automated-ultramicrotomy/embl-system/Images/box-images/box-1.jpg

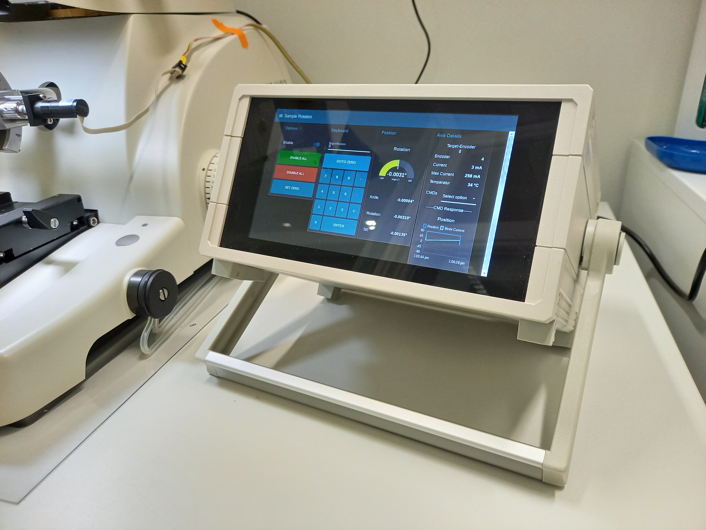
Images/box-images/box-1.jpg
