automated-ultramicrotomy/embl-system/Images/box-images/box-2.jpg

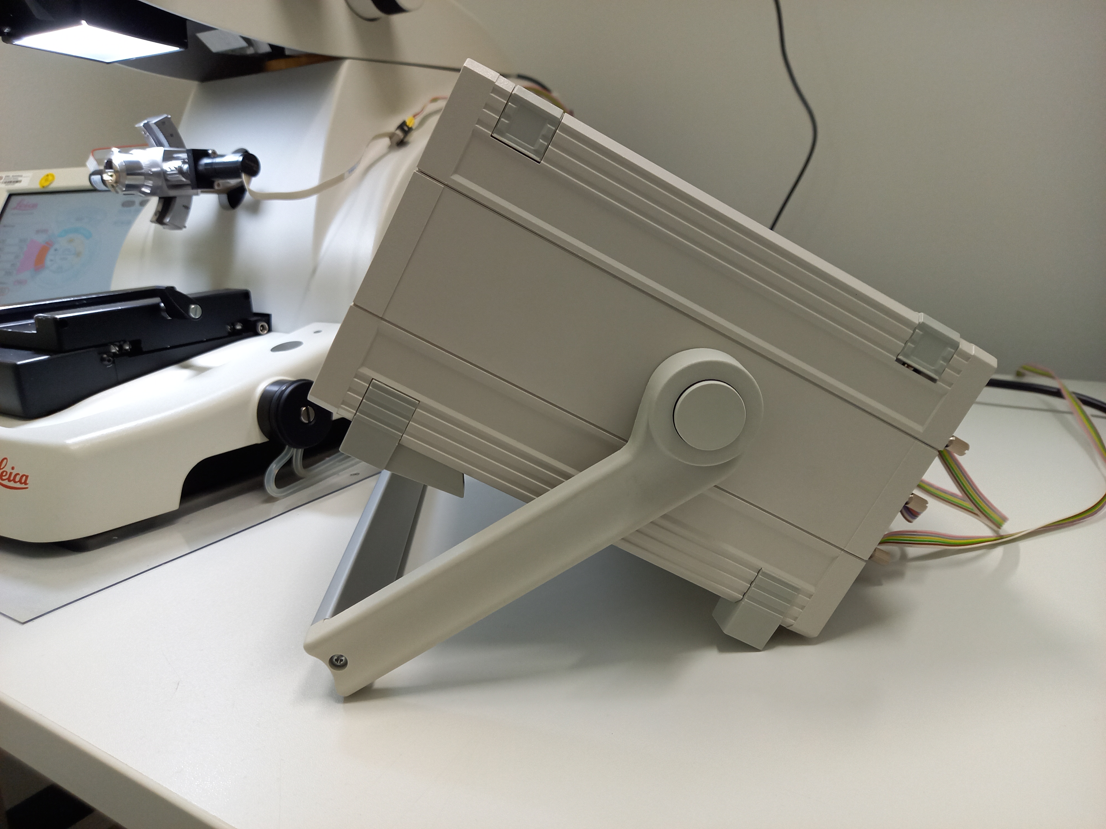
Images/box-images/box-2.jpg
