automated-ultramicrotomy/embl-system/Images/box-images/box-3.jpg

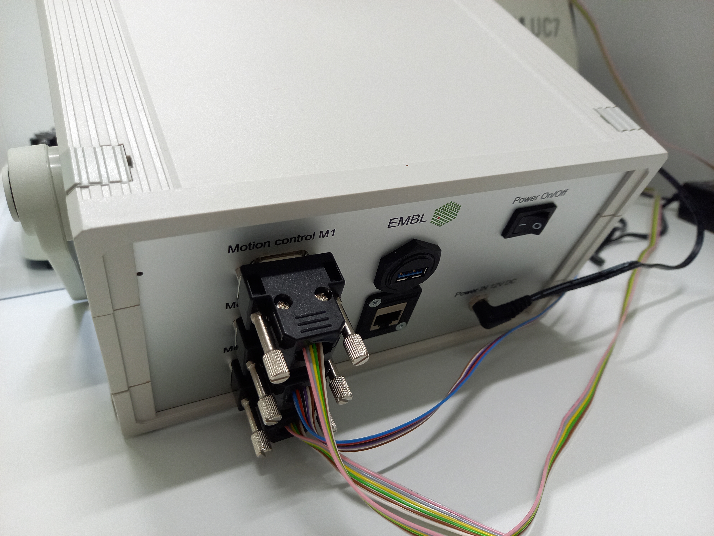
Images/box-images/box-3.jpg
