automated-ultramicrotomy/embl-system/Images/box-images/inside-the-box.jpg

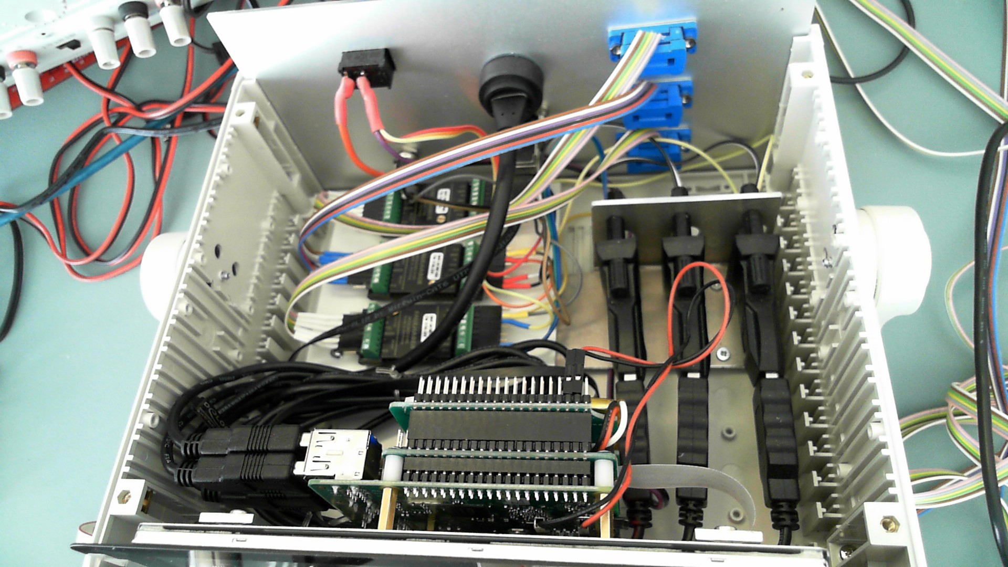
Images/box-images/inside-the-box.jpg
