automated-ultramicrotomy/embl-system/Images/knife-tilt/knife-motor.png

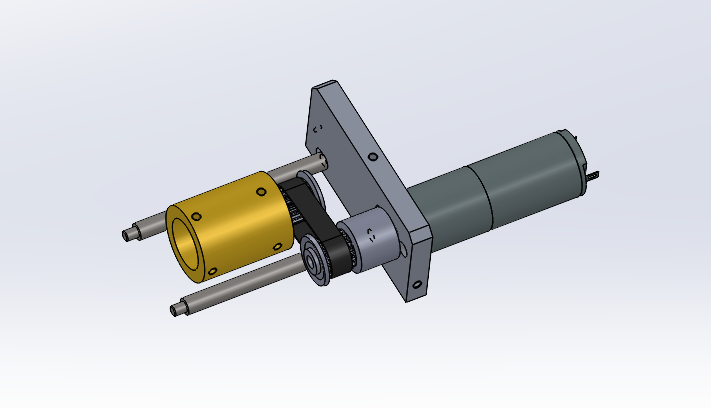
Images/knife-tilt/knife-motor.png
