automated-ultramicrotomy/embl-system/Images/knife-tilt/knife-tilt.jpg

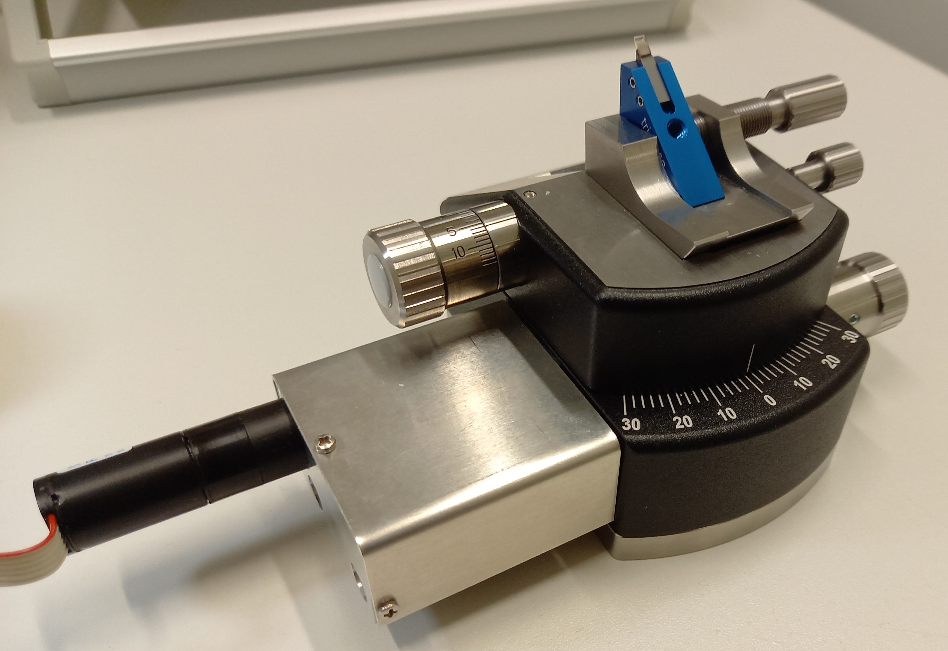
Images/knife-tilt/knife-tilt.jpg
