automated-ultramicrotomy/embl-system/Images/knife-tilt/knife.png

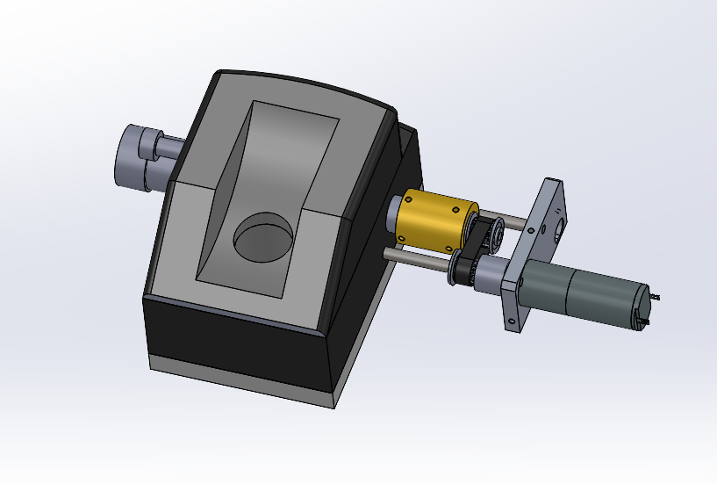
Images/knife-tilt/knife.png
