automated-ultramicrotomy/embl-system/Images/knife-tilt/knife_underside.jpg

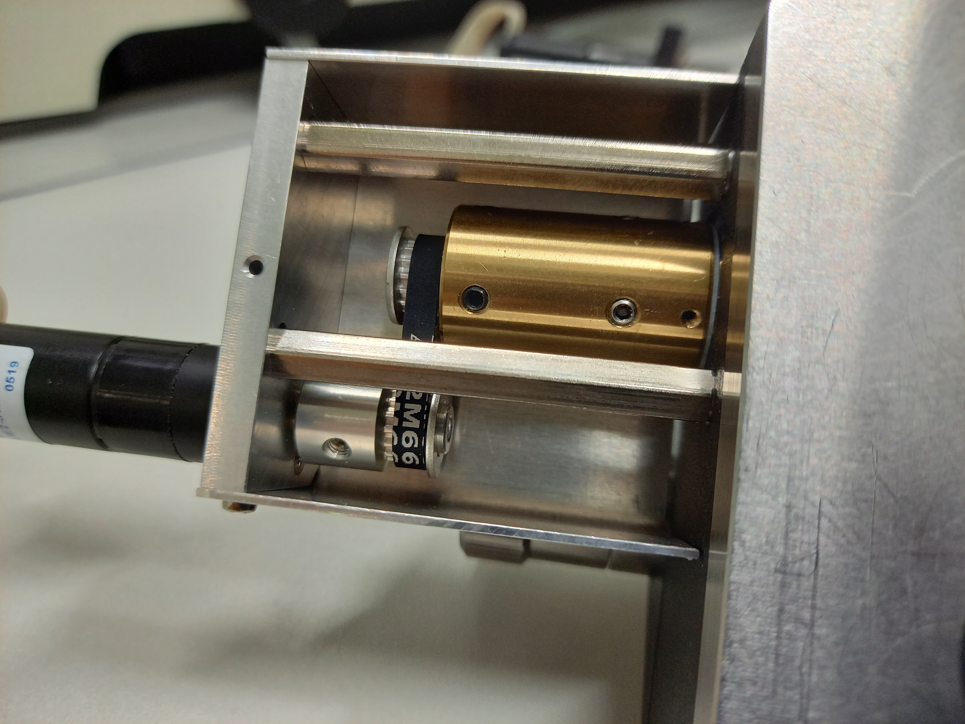
Images/knife-tilt/knife_underside.jpg
