automated-ultramicrotomy/embl-system/Images/knife-tilt/knife_underside_2.jpg

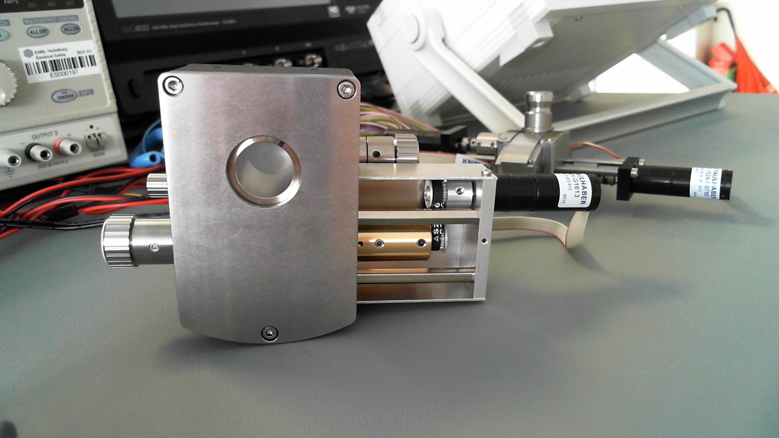
Images/knife-tilt/knife_underside_2.jpg
