automated-ultramicrotomy/embl-system/Images/sample-tilt-rotation/arc_closeup.jpg

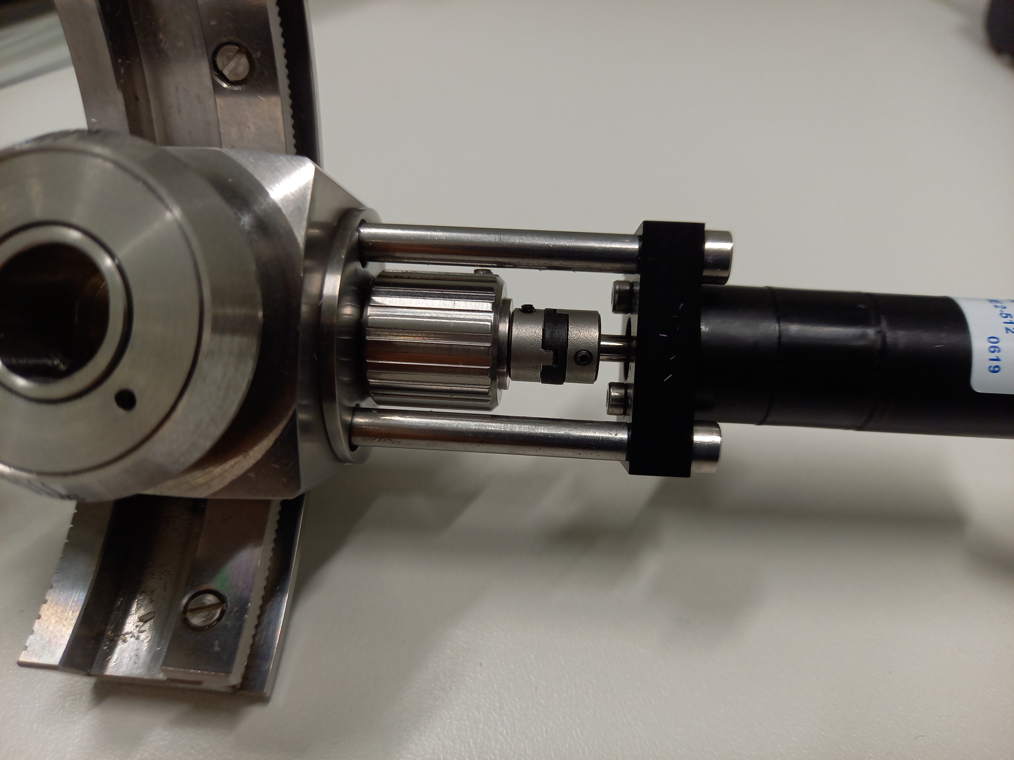
Images/sample-tilt-rotation/arc_closeup.jpg
