automated-ultramicrotomy/embl-system/Images/sample-tilt-rotation/arc_closeup_2.jpg

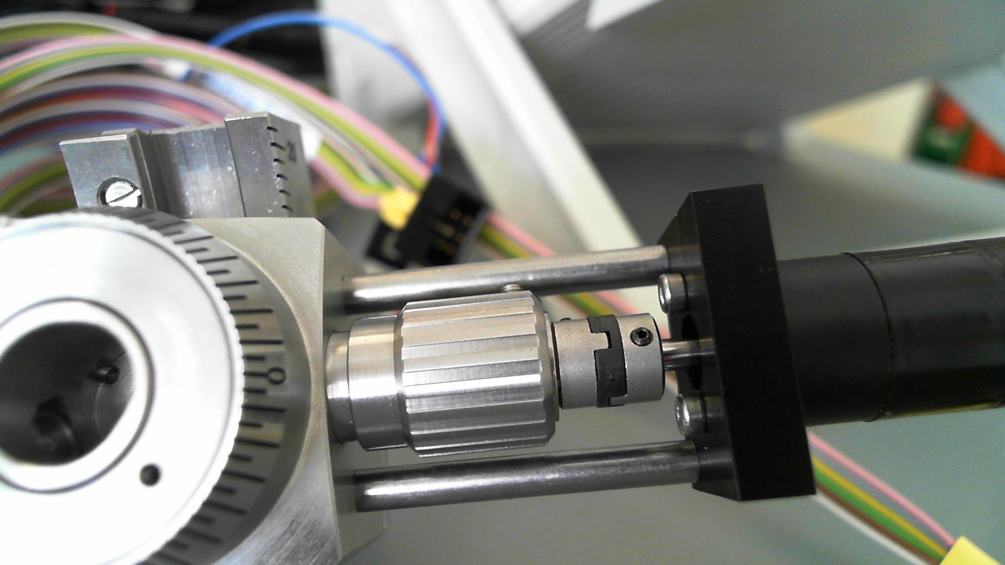
Images/sample-tilt-rotation/arc_closeup_2.jpg
