automated-ultramicrotomy/embl-system/Images/sample-tilt-rotation/arc_closeup_3.jpg

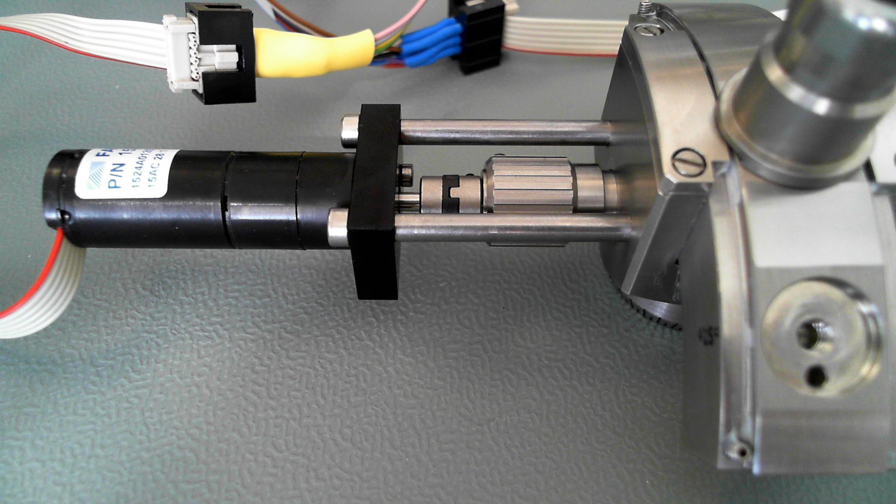
Images/sample-tilt-rotation/arc_closeup_3.jpg
