automated-ultramicrotomy/embl-system/Images/sample-tilt-rotation/arc_front_1.jpg

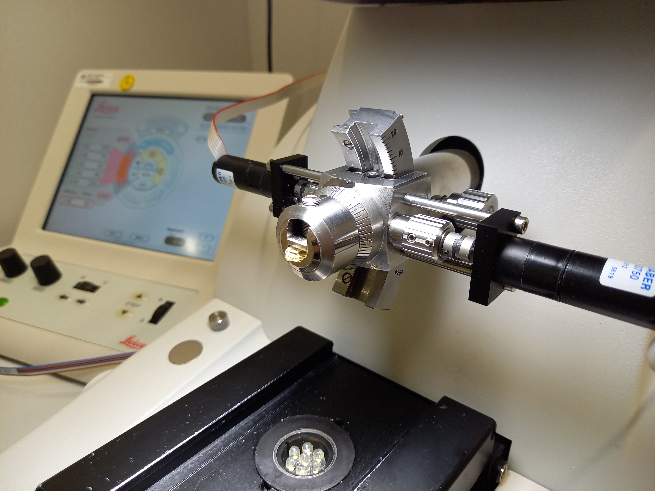
Images/sample-tilt-rotation/arc_front_1.jpg
