automated-ultramicrotomy/embl-system/Images/sample-tilt-rotation/arc_front_2.jpg

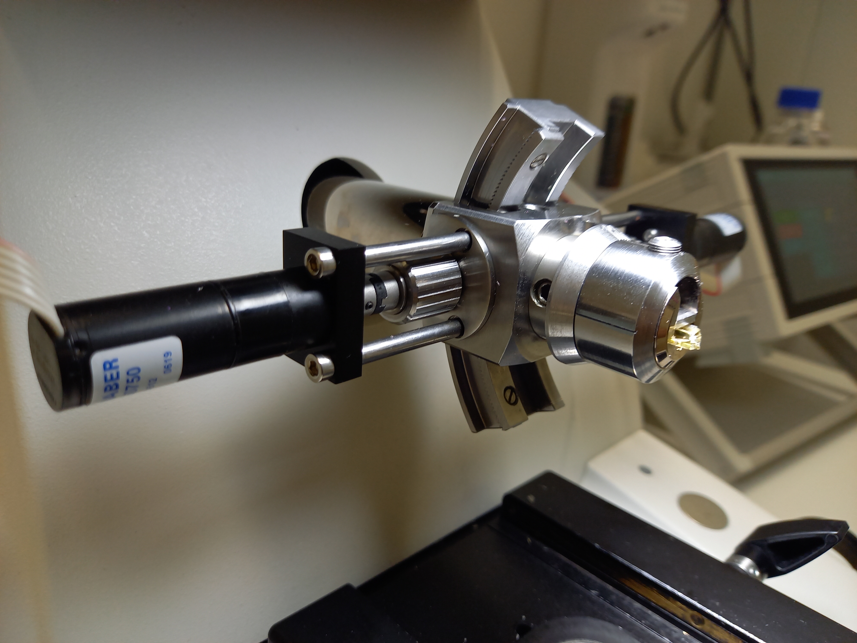
Images/sample-tilt-rotation/arc_front_2.jpg
