automated-ultramicrotomy/embl-system/Images/sample-tilt-rotation/segment-motor.png

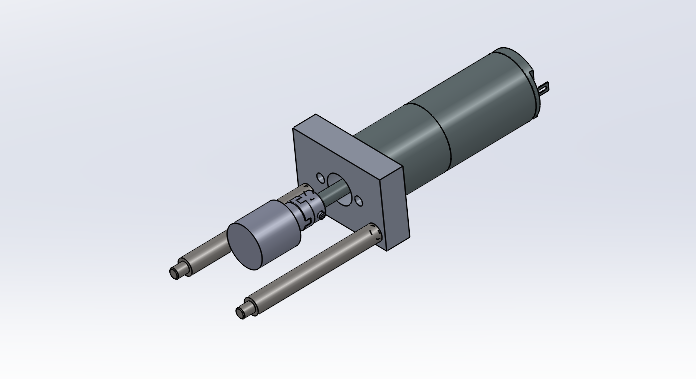
Images/sample-tilt-rotation/segment-motor.png
