automated-ultramicrotomy/embl-system/Images/sample-tilt-rotation/segment.png

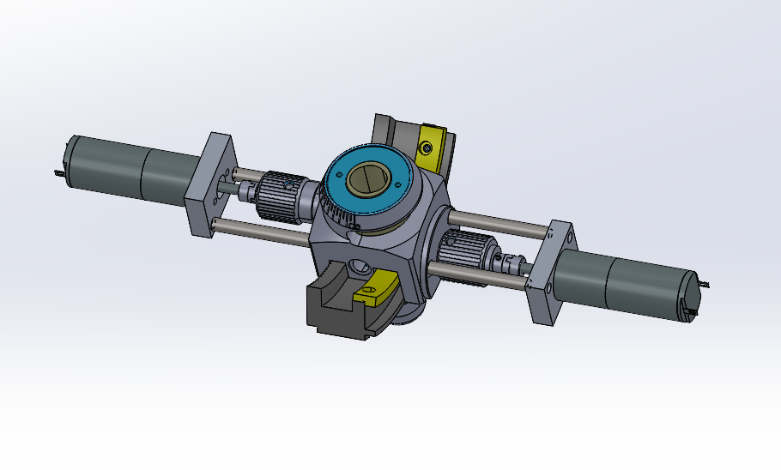
Images/sample-tilt-rotation/segment.png
