automated-ultramicrotomy/embl-system/Images/user-interface/node-red-flows/NodRed_Axis_Logic.PNG

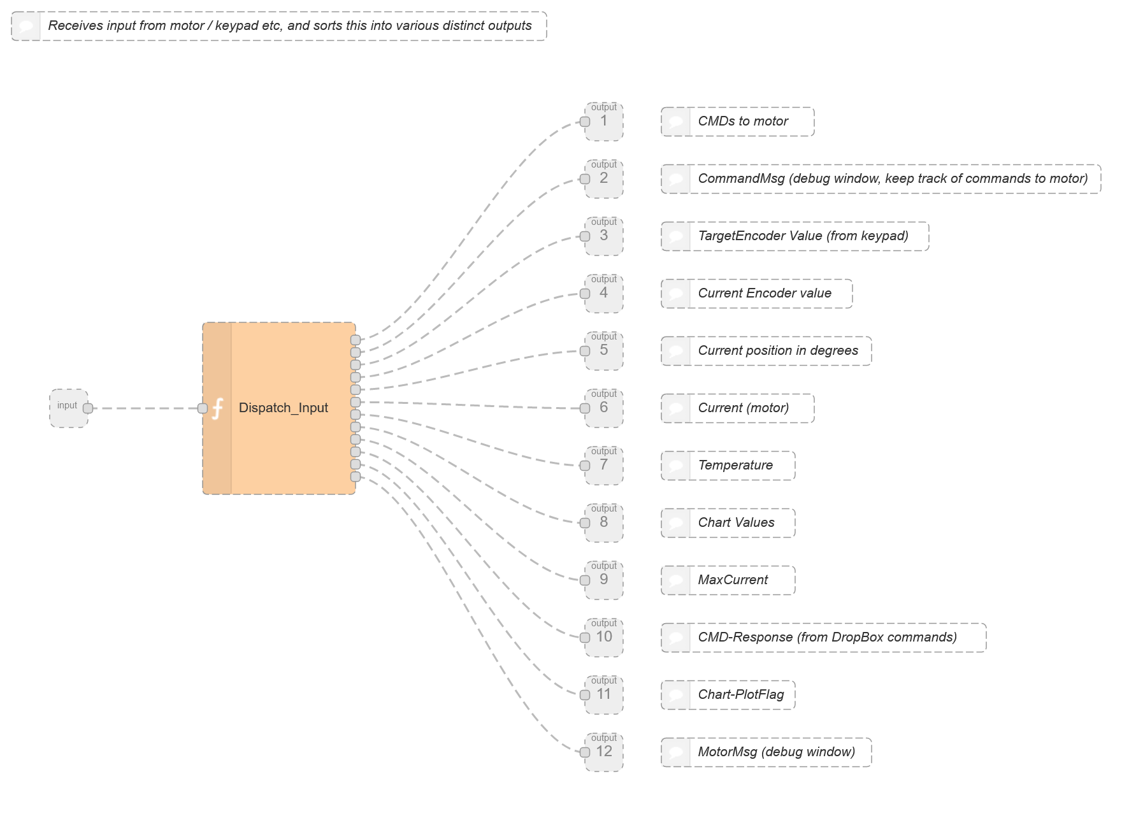
Images/user-interface/node-red-flows/NodRed_Axis_Logic.PNG
