automated-ultramicrotomy/embl-system/Images/user-interface/node-red-flows/NodRed_close.PNG

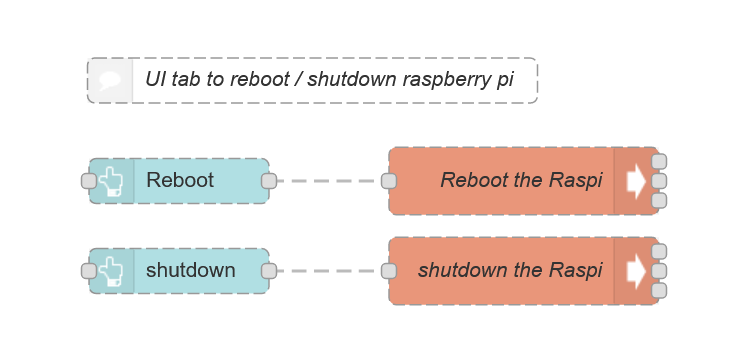
Images/user-interface/node-red-flows/NodRed_close.PNG
