automated-ultramicrotomy/embl-system/Images/user-interface/node-red-flows/NodRed_KnifeTilt.PNG

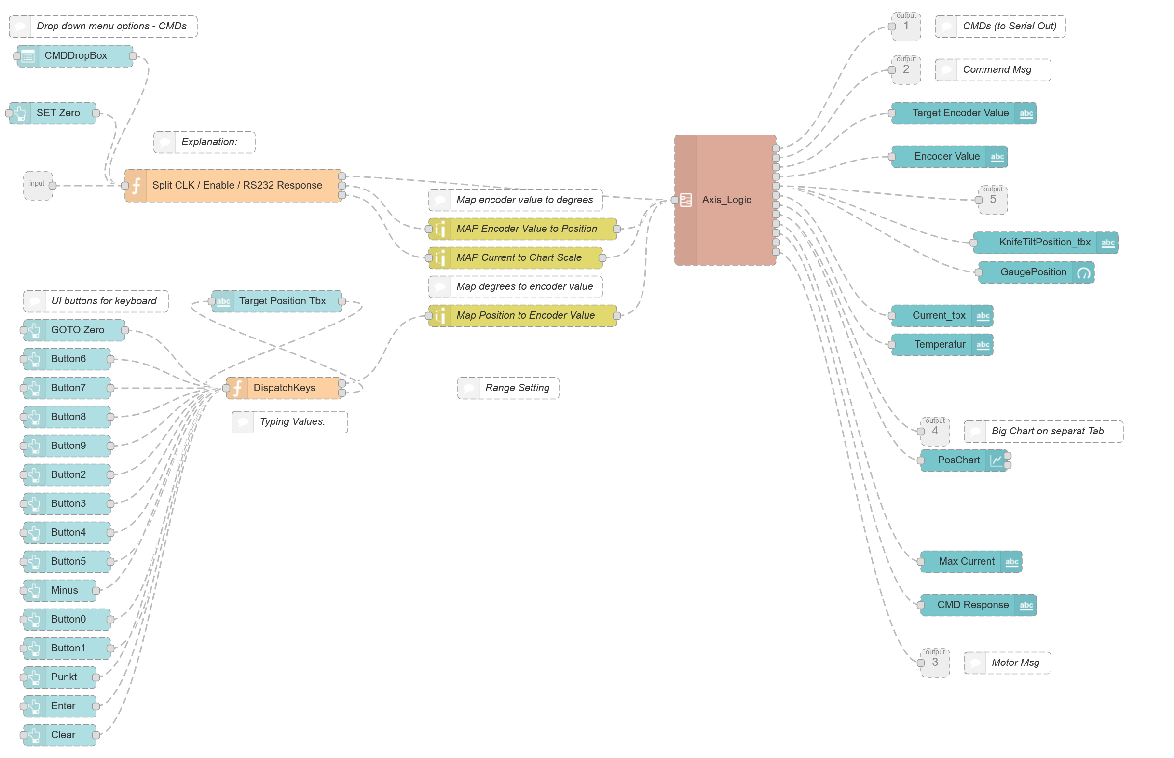
Images/user-interface/node-red-flows/NodRed_KnifeTilt.PNG
