automated-ultramicrotomy/embl-system/Images/user-interface/node-red-flows/NodRed_main_2.PNG

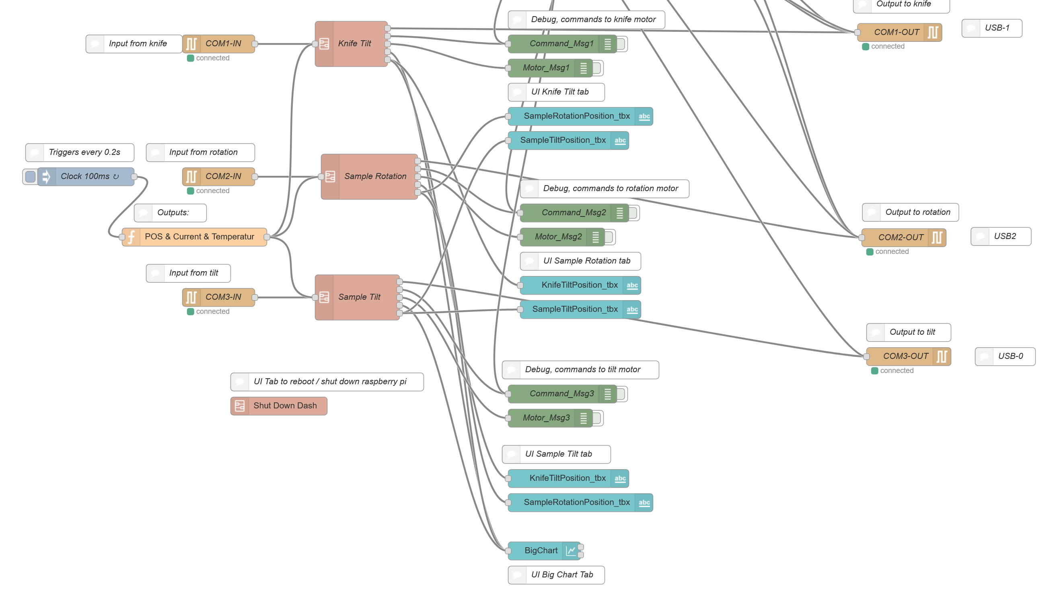
Images/user-interface/node-red-flows/NodRed_main_2.PNG
