automated-ultramicrotomy/embl-system/Images/user-interface/node-red-flows/NodRed_sample_rotation.PNG

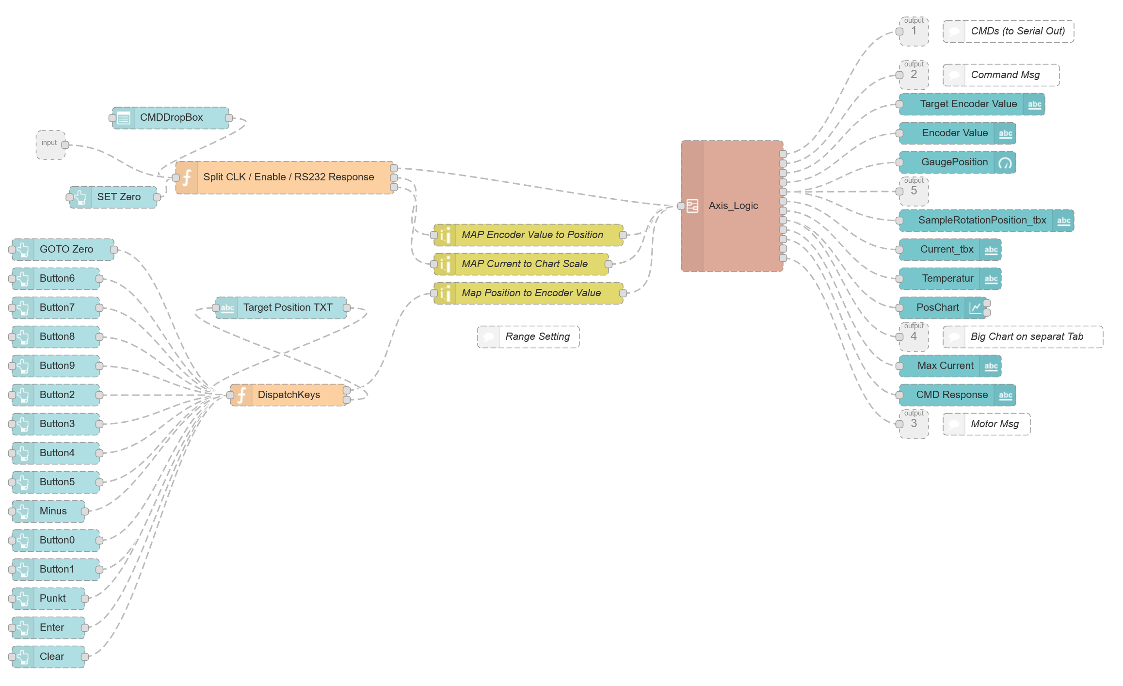
Images/user-interface/node-red-flows/NodRed_sample_rotation.PNG
