automated-ultramicrotomy/embl-system/Images/user-interface/node-red-flows/NodRed_Sample_Tilt.PNG

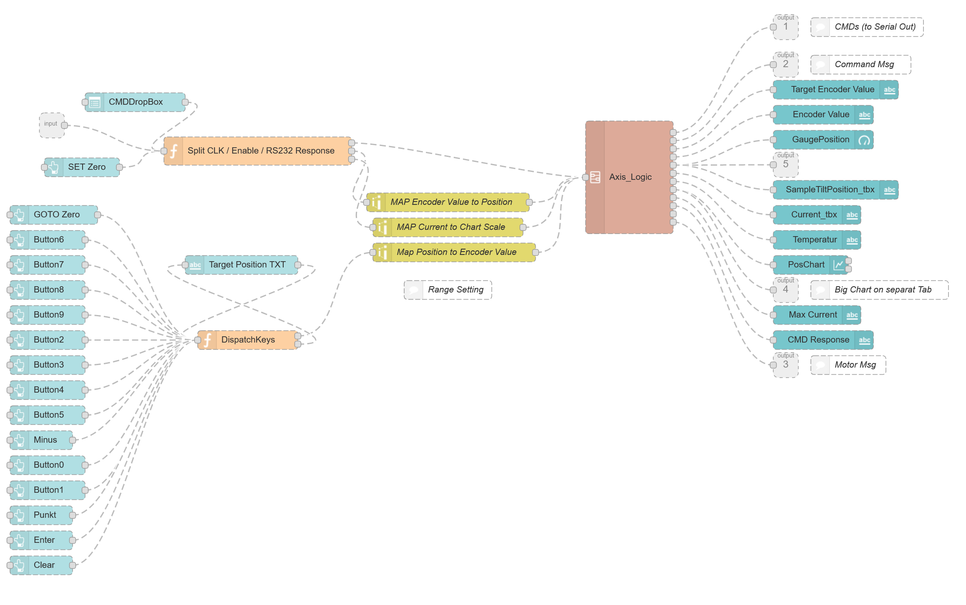
Images/user-interface/node-red-flows/NodRed_Sample_Tilt.PNG
