automated-ultramicrotomy/embl-system/Images/user-interface/ui_images/Capture_KnifeTilt.PNG

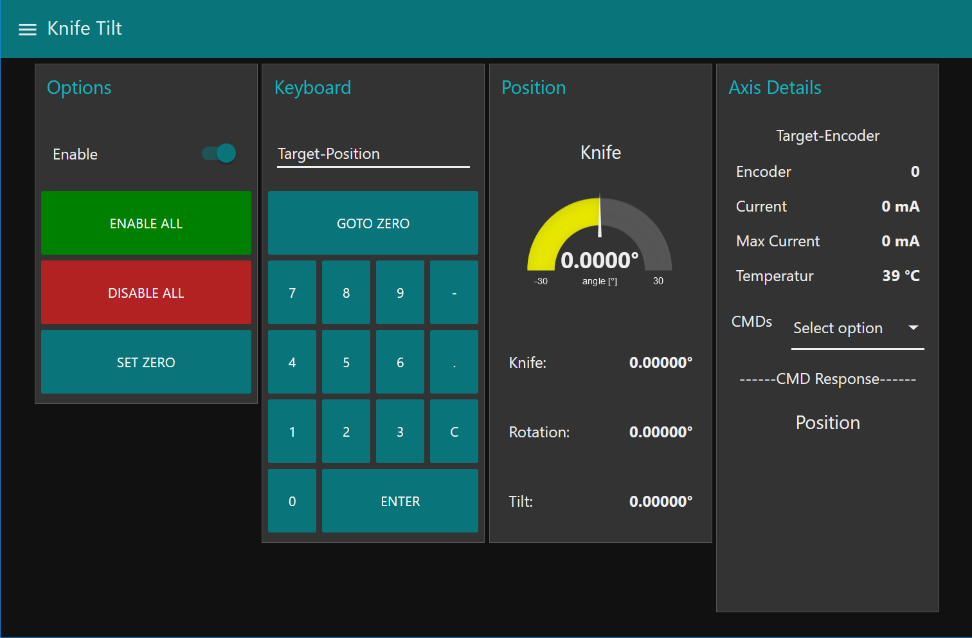
Images/user-interface/ui_images/Capture_KnifeTilt.PNG
