automated-ultramicrotomy/embl-system/Images/user-interface/ui_images/Capture_Power.PNG

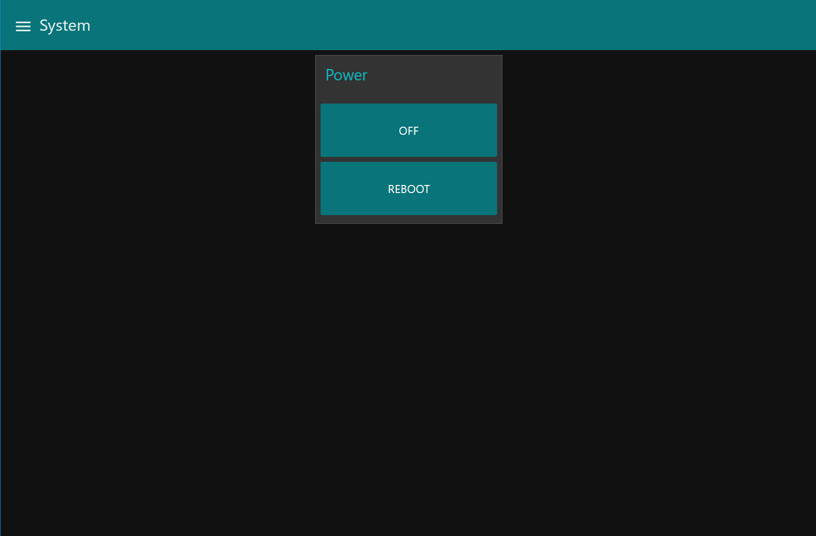
Images/user-interface/ui_images/Capture_Power.PNG
