automated-ultramicrotomy/embl-system/Images/user-interface/ui_images/Capture_SampleRotation.PNG

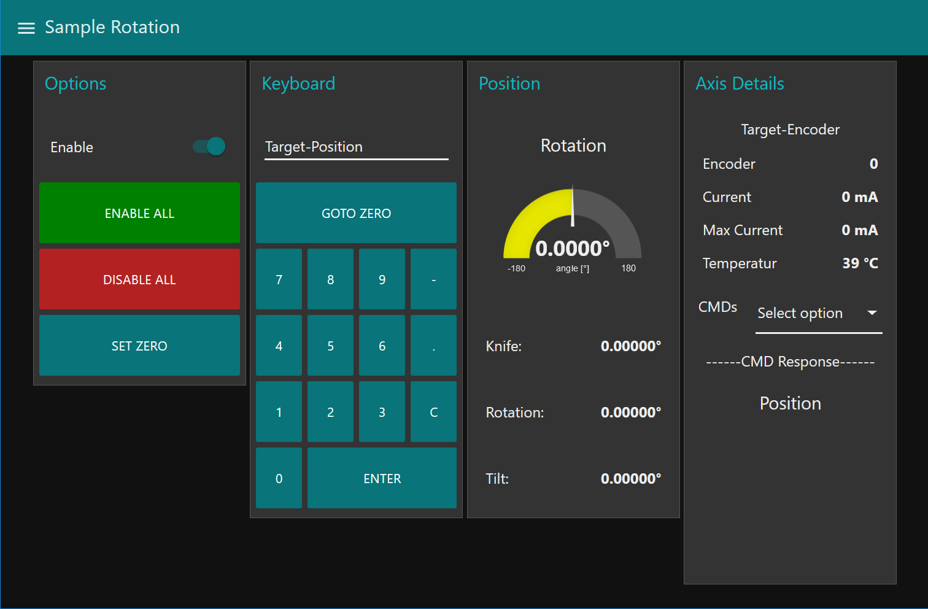
Images/user-interface/ui_images/Capture_SampleRotation.PNG
