automated-ultramicrotomy/embl-system/CAD Parts/Solidworks 2022 Models/knife-tilt/motor-mount/OTS/HTPA15S2M060-K-H3.stp

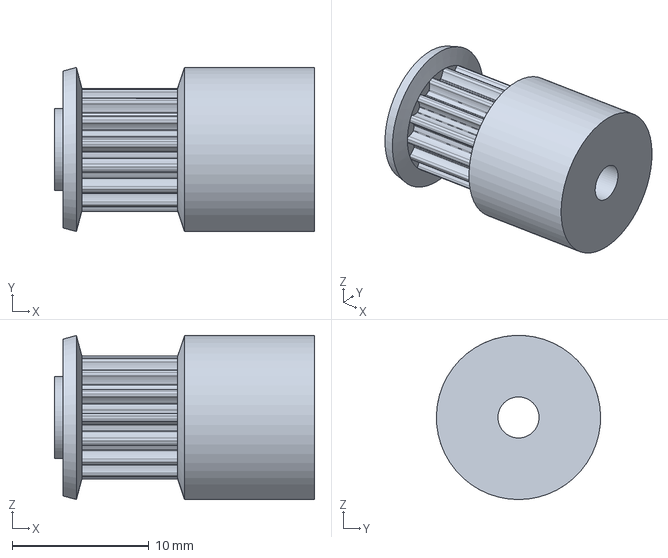
[picture p46: CAD file, 2023-07-30]
CAD Parts/Solidworks 2022 Models/knife-tilt/motor-mount/OTS/HTPA15S2M060-K-H3.stp
19.0 x 12.0 x 12.0 mm
