automated-ultramicrotomy/embl-system/CAD Parts/Solidworks 2022 Models/sample-tilt-rotation/motor-mount/50-AL/50-AL-0001-00.SLDPRT

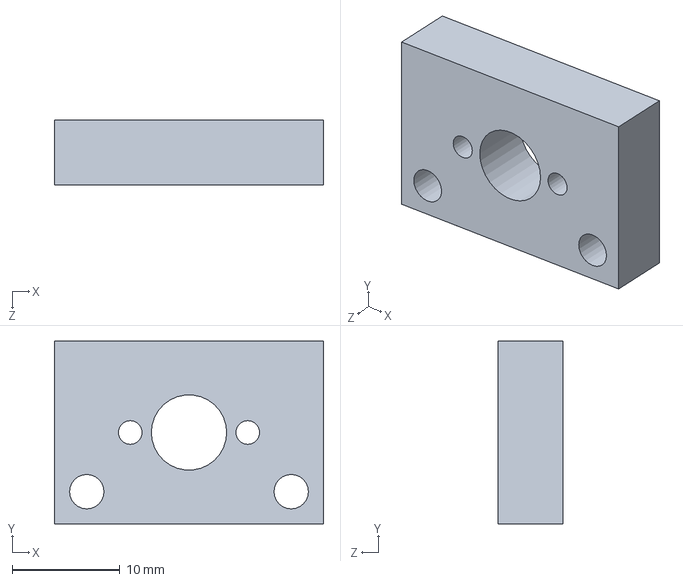
[picture p47: CAD file, 2023-07-30]
CAD Parts/Solidworks 2022 Models/sample-tilt-rotation/motor-mount/50-AL/50-AL-0001-00.SLDPRT
25.0 x 17.0 x 6.00 mm
