automated-ultramicrotomy/embl-system/CAD Parts/Solidworks 2022 Models/sample-tilt-rotation/motor-mount/OTS/1524T_SR.SLDPRT

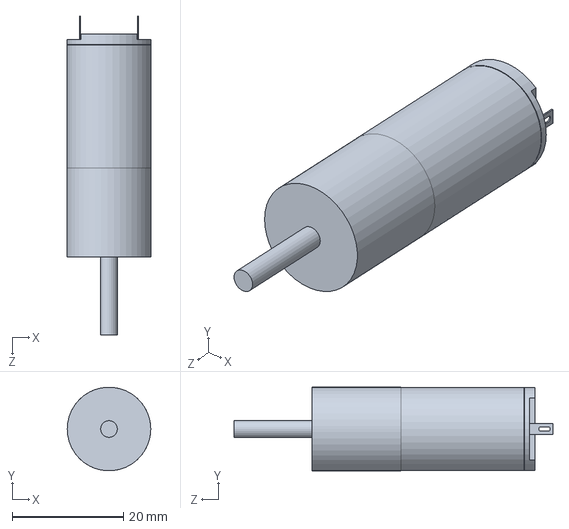
[picture p48: CAD file, 2023-07-30]
CAD Parts/Solidworks 2022 Models/sample-tilt-rotation/motor-mount/OTS/1524T_SR.SLDPRT
15.0 x 15.0 x 57.2 mm
