automated-ultramicrotomy/embl-system/CAD Parts/STEP Models/calibration/30-YS-0004-00.STEP

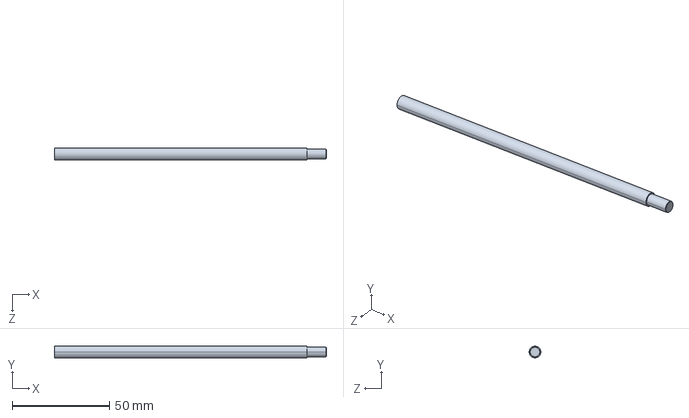
[picture p49: CAD file, 2022-05-09]
CAD Parts/STEP Models/calibration/30-YS-0004-00.STEP
140.0 x 6.00 x 6.00 mm
