automated-ultramicrotomy/embl-system/CAD Parts/Solidworks 2022 Models/Calibration/30-YS/30-YS-0003-00.SLDPRT

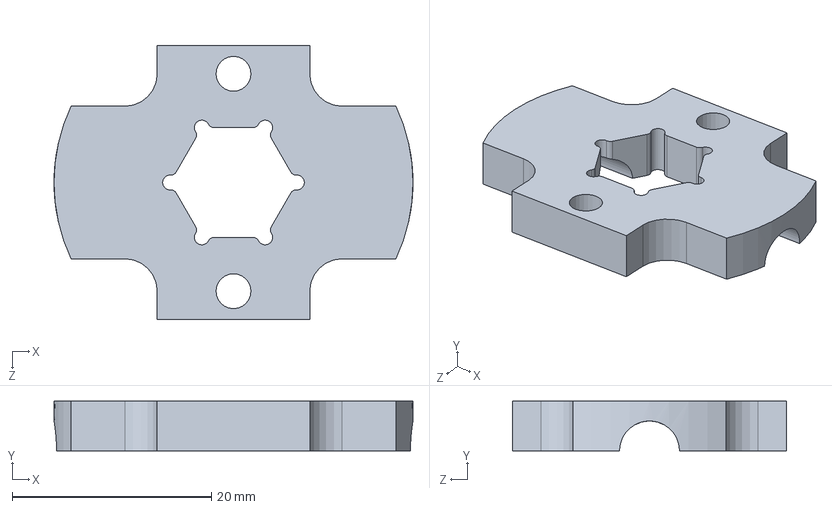
[picture p50: CAD file, 2023-07-30]
CAD Parts/Solidworks 2022 Models/Calibration/30-YS/30-YS-0003-00.SLDPRT
36.0 x 5.00 x 27.5 mm
