automated-ultramicrotomy/embl-system/CAD Parts/Solidworks 2022 Models/knife-tilt/motor-mount/50-AL/50-AL-0004-00.SLDPRT

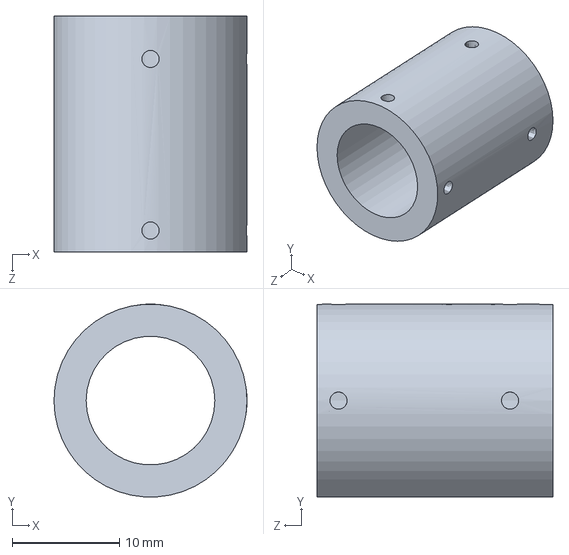
[picture p51: CAD file, 2023-07-30]
CAD Parts/Solidworks 2022 Models/knife-tilt/motor-mount/50-AL/50-AL-0004-00.SLDPRT
18.0 x 18.0 x 22.0 mm
