automated-ultramicrotomy/embl-system/CAD Parts/Solidworks 2022 Models/Calibration/30-YS/30-YS-0007-00.SLDPRT

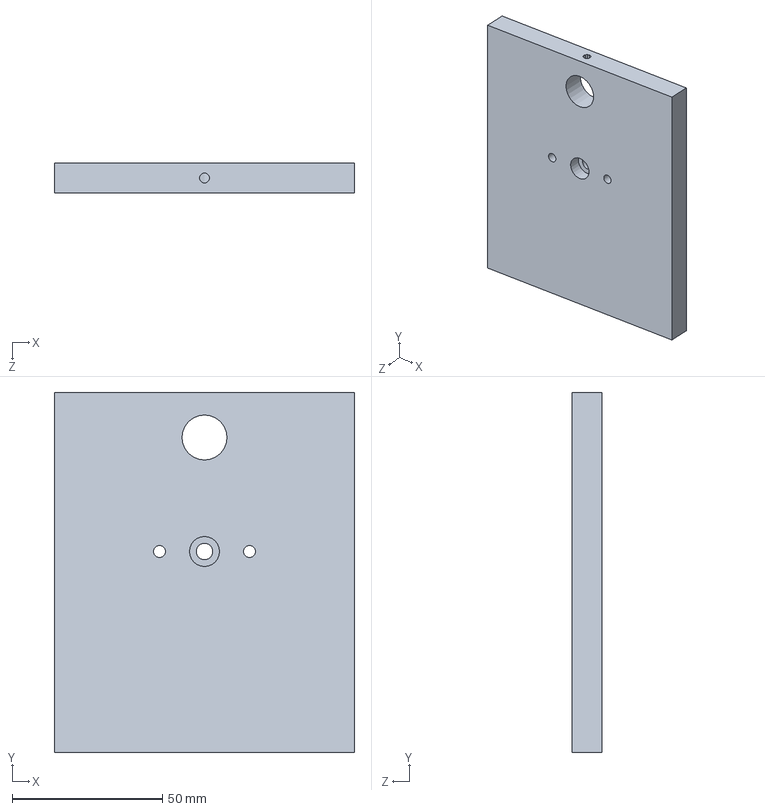
[picture p52: CAD file, 2023-07-30]
CAD Parts/Solidworks 2022 Models/Calibration/30-YS/30-YS-0007-00.SLDPRT
100.0 x 120.0 x 10.0 mm
