automated-ultramicrotomy/embl-system/CAD Parts/STEP Models/calibration/30-YS-0006-00.STEP

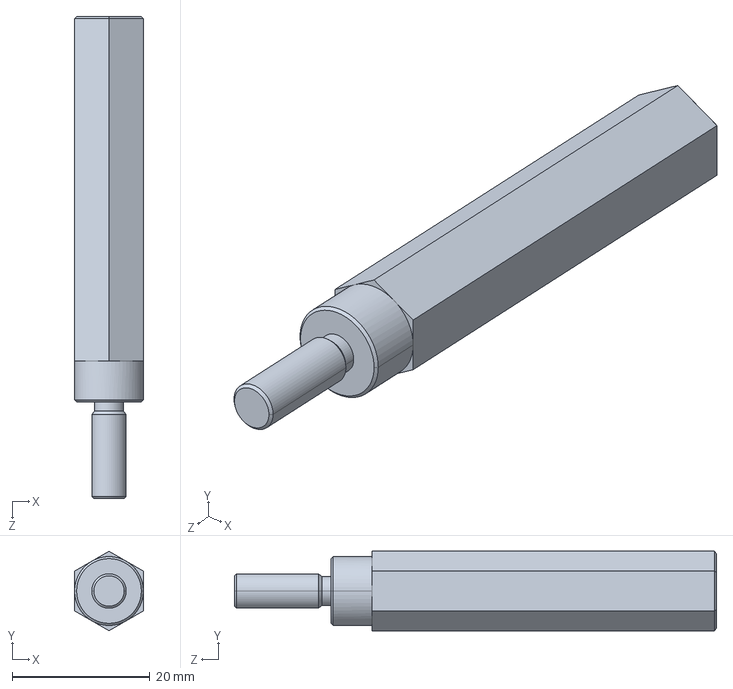
[picture p54: CAD file, 2022-05-09]
CAD Parts/STEP Models/calibration/30-YS-0006-00.STEP
10.0 x 11.5 x 70.0 mm
