automated-ultramicrotomy/embl-system/CAD Parts/Solidworks 2022 Models/sample-tilt-rotation/sample-arc/Segmentbogen/16-708-031-109-Z-0000.stp.SLDPRT

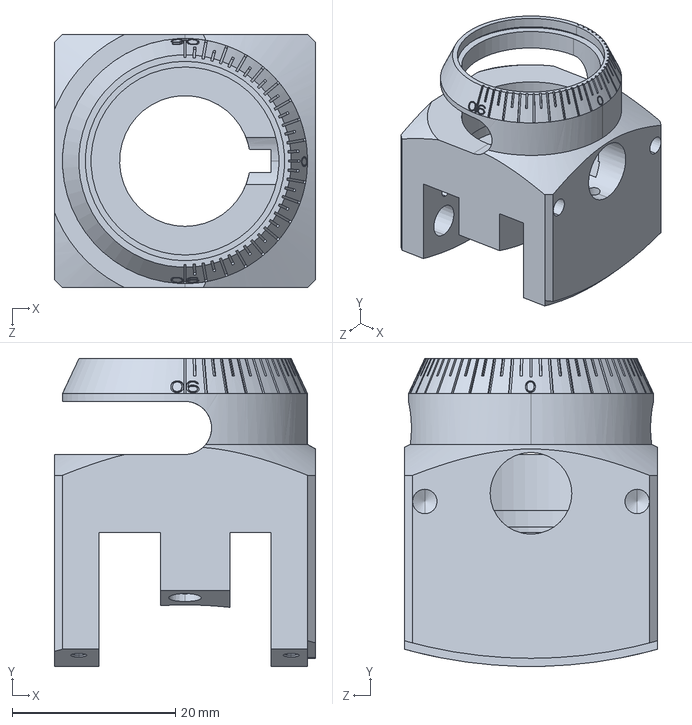
[picture p55: CAD file, 2023-07-30]
CAD Parts/Solidworks 2022 Models/sample-tilt-rotation/sample-arc/Segmentbogen/16-708-031-109-Z-0000.stp.SLDPRT
32.0 x 37.7 x 31.0 mm
