automated-ultramicrotomy/embl-system/Images/calibration/knife-tilt-images/knife-calibration-2.jpg

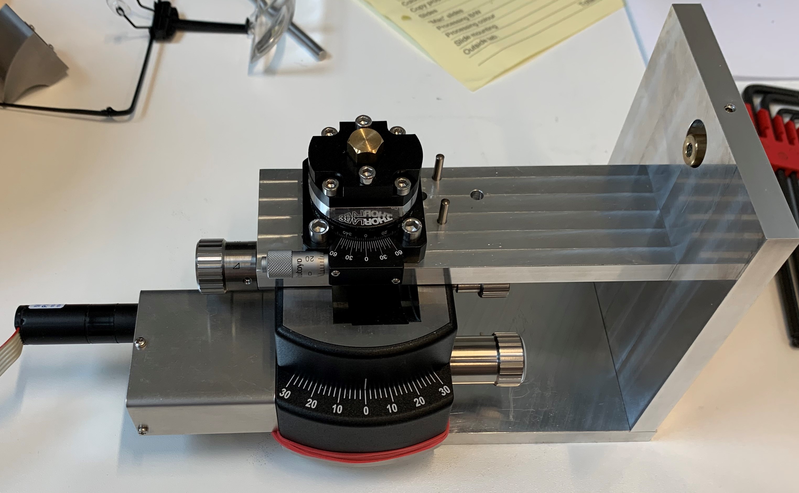
Images/calibration/knife-tilt-images/knife-calibration-2.jpg
