automated-ultramicrotomy/embl-system/Images/calibration/sample-rotation-images/sample-rotation-1.JPG

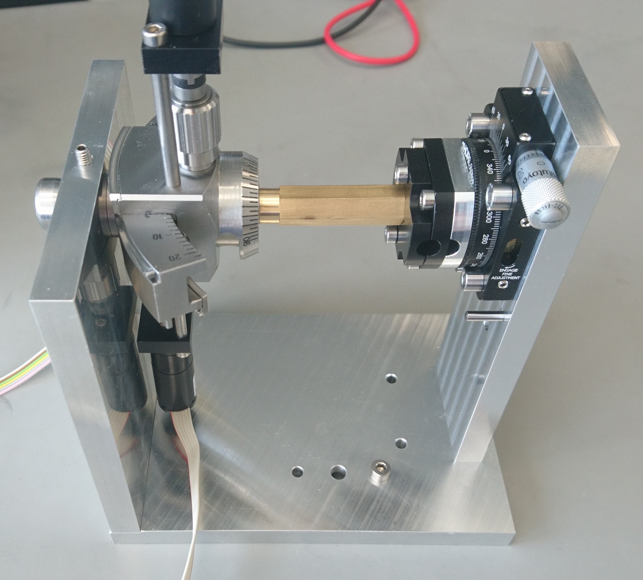
Images/calibration/sample-rotation-images/sample-rotation-1.JPG
