automated-ultramicrotomy/embl-system/Images/calibration/sample-rotation-images/sample-rotation-2.JPG

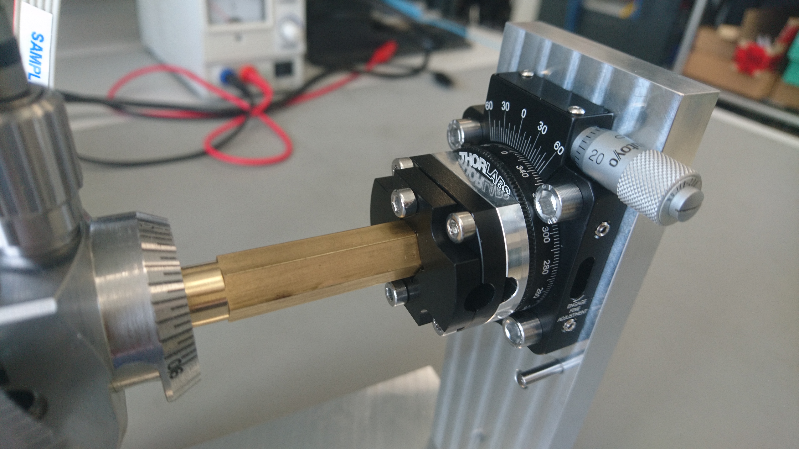
Images/calibration/sample-rotation-images/sample-rotation-2.JPG
