automated-ultramicrotomy/embl-system/Images/calibration/sample-rotation-images/sample-rotation-3.JPG

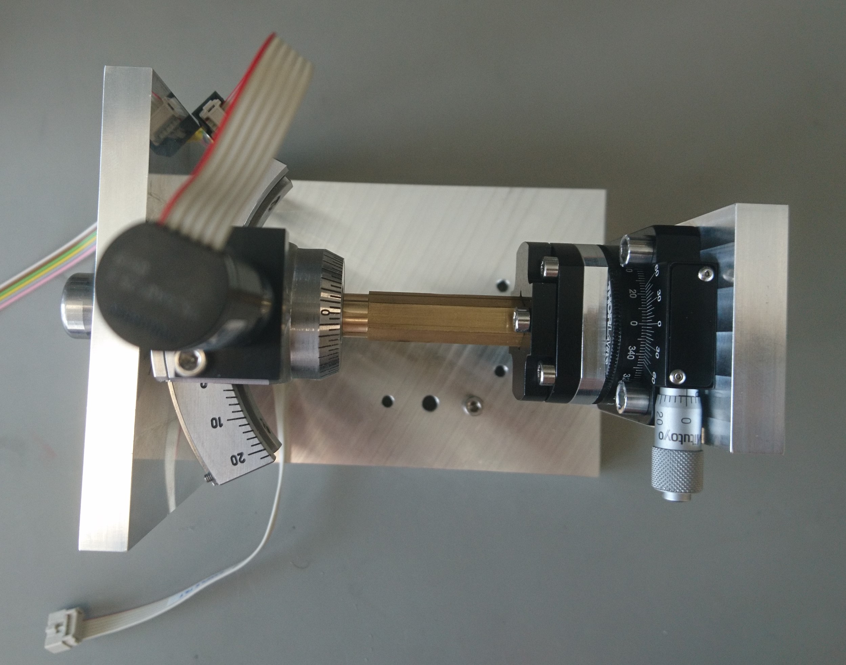
Images/calibration/sample-rotation-images/sample-rotation-3.JPG
