automated-ultramicrotomy/embl-system/Images/calibration/sample-tilt-images/sample-tilt-1.jpg

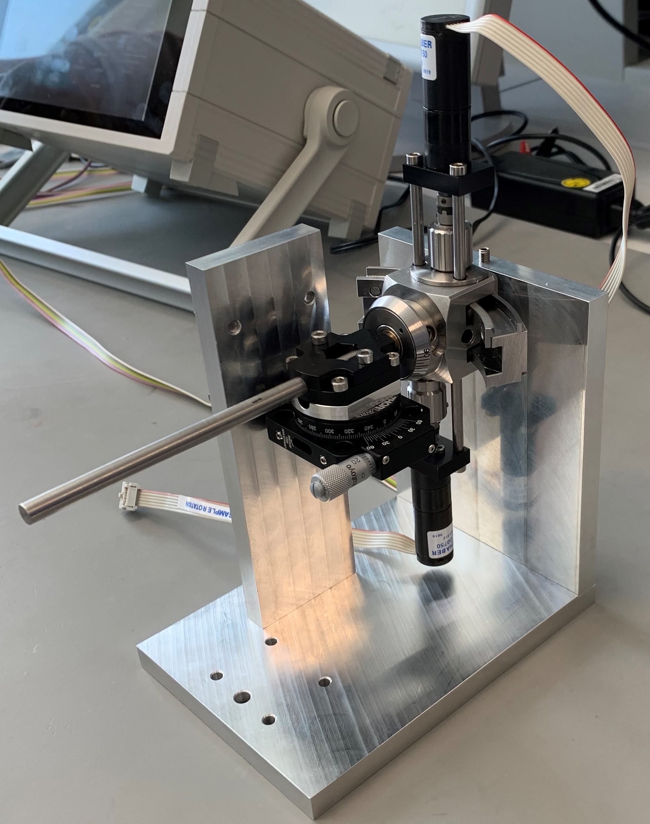
Images/calibration/sample-tilt-images/sample-tilt-1.jpg
