automated-ultramicrotomy/embl-system/Images/calibration/sample-tilt-images/sample-tilt-2.jpg

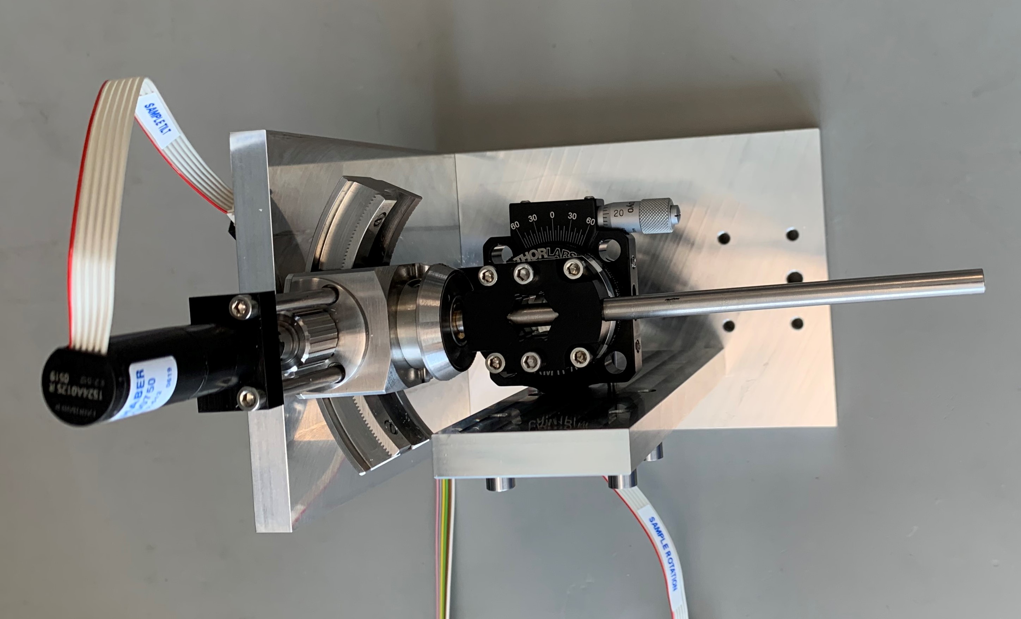
Images/calibration/sample-tilt-images/sample-tilt-2.jpg
