automated-ultramicrotomy/embl-system/Images/calibration/sample-tilt-images/sample-tilt-diagram-1.png

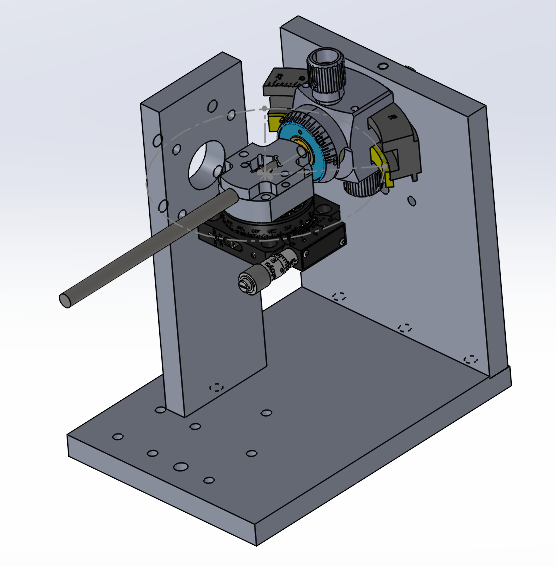
Images/calibration/sample-tilt-images/sample-tilt-diagram-1.png
