automated-ultramicrotomy/embl-system/Images/calibration/sample-tilt-images/sample-tilt-diagram-2.png

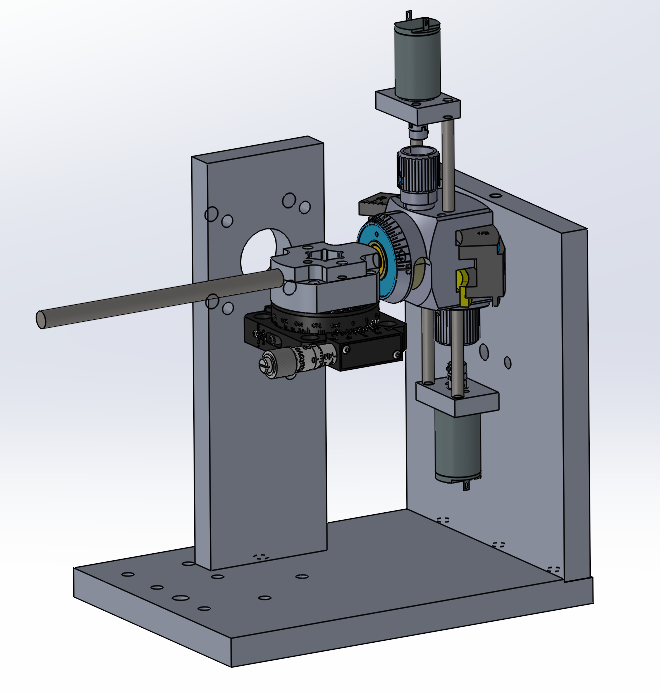
Images/calibration/sample-tilt-images/sample-tilt-diagram-2.png
